sparkfun/SparkFun_LTE_Stick_LARA_R6/docs/assets/img/m-center_ports.jpg

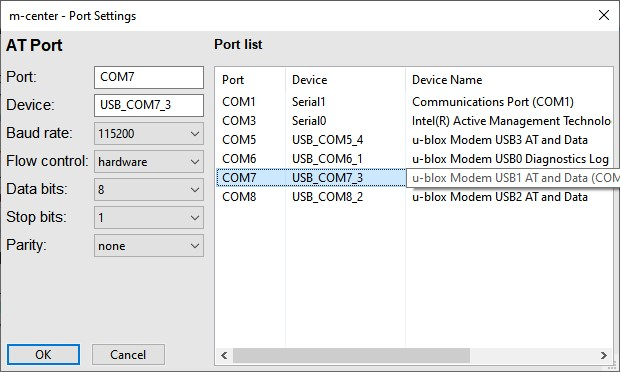
docs/assets/img/m-center_ports.jpg
